FabianGundel/pid-temperature-controller/docs/calibration.kicad_sch

## KiCad design docs/calibration.kicad_sch (2026-05-13)

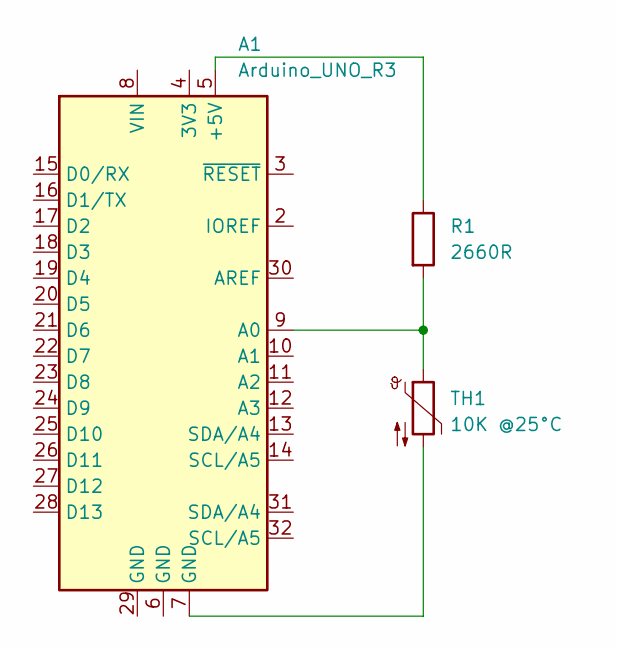
[picture p3: schematic calibration.kicad_sch]

Parts:
A1: Arduino_UNO_R3
R1: 2660R
TH1: 10K @25°C

Connections:
unnamed: A1.5 (+5V), R1.1
unnamed: A1.7 (GND), TH1.2
unnamed: A1.9 (A0), R1.2, TH1.1
