FabianGundel/pid-temperature-controller/docs/main.kicad_sch

## KiCad design docs/main.kicad_sch (2026-05-13)

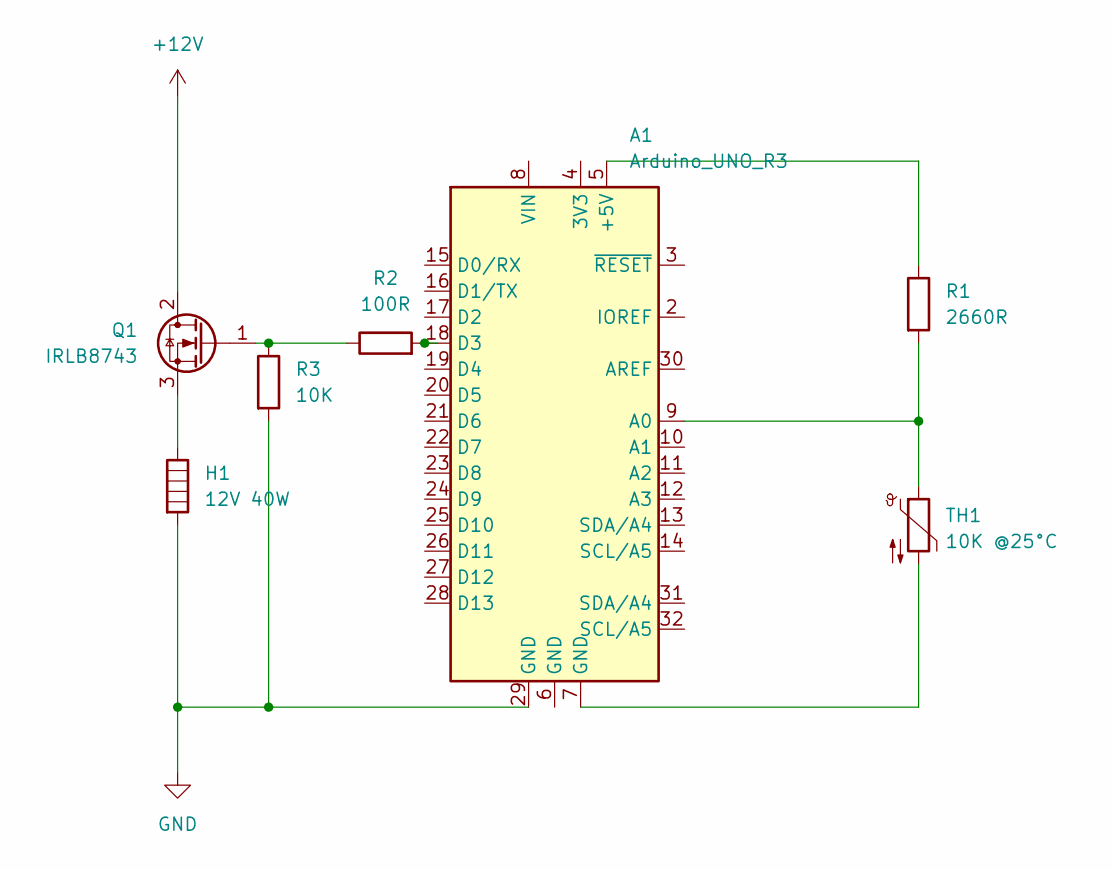
[picture p4: schematic main.kicad_sch]

Parts:
A1: Arduino_UNO_R3
H1: 12V 40W
Q1: IRLB8743
R1: 2660R
R2: 100R
R3: 10K
TH1: 10K @25°C

Connections:
+12V: Q1.2 (D)
GND: A1.29 (GND), H1.2, R3.2
unnamed: A1.5 (+5V), R1.1
unnamed: A1.7 (GND), TH1.2
unnamed: A1.9 (A0), R1.2, TH1.1
unnamed: A1.18 (D3), R2.2
unnamed: H1.1, Q1.3 (S)
unnamed: Q1.1 (G), R2.1, R3.1
